pakornpiam/kumiko-lamp/stl/modern_shade_bishamon_kikkou.stl

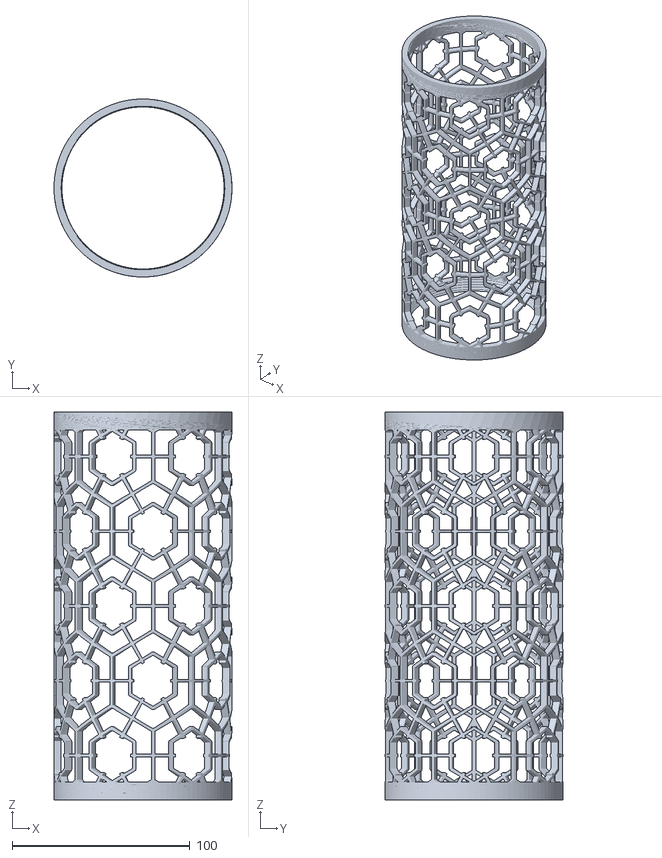
[picture p17: CAD file, 2026-08-05]
stl/modern_shade_bishamon_kikkou.stl
100.0 x 100.0 x 218.0
