pakornpiam/kumiko-lamp/stl/finial.stl

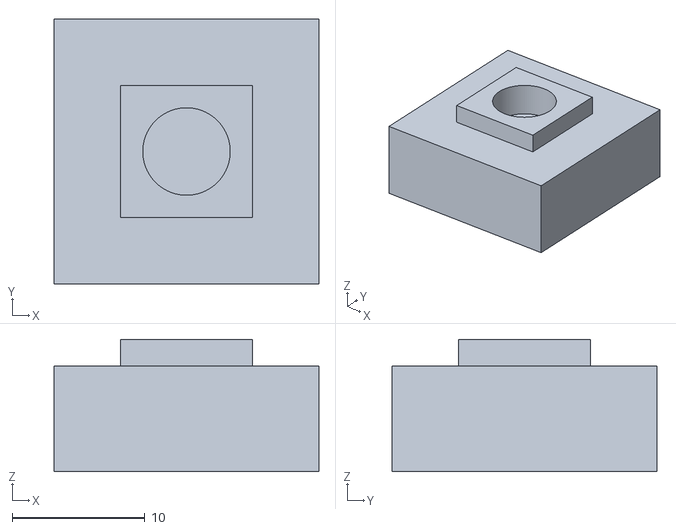
[picture p18: CAD file, 2026-08-05]
stl/finial.stl
20.0 x 20.0 x 10.0
