pakornpiam/kumiko-lamp/stl/panel_masu.stl

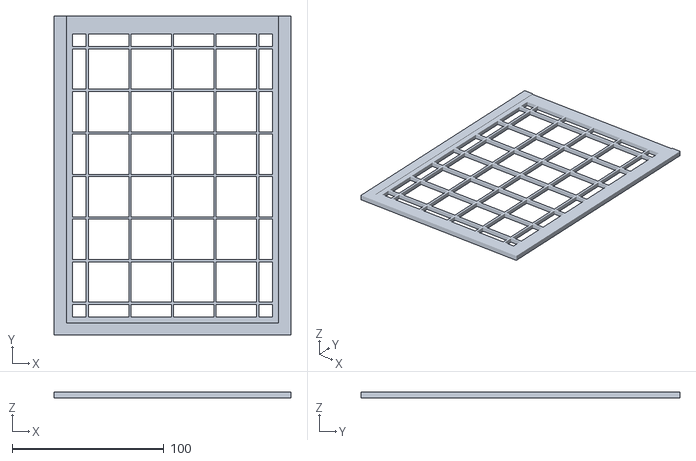
[picture p19: CAD file, 2026-08-03]
stl/panel_masu.stl
155.7 x 210.0 x 4.00
