pakornpiam/kumiko-lamp/stl/panel_senbon.stl

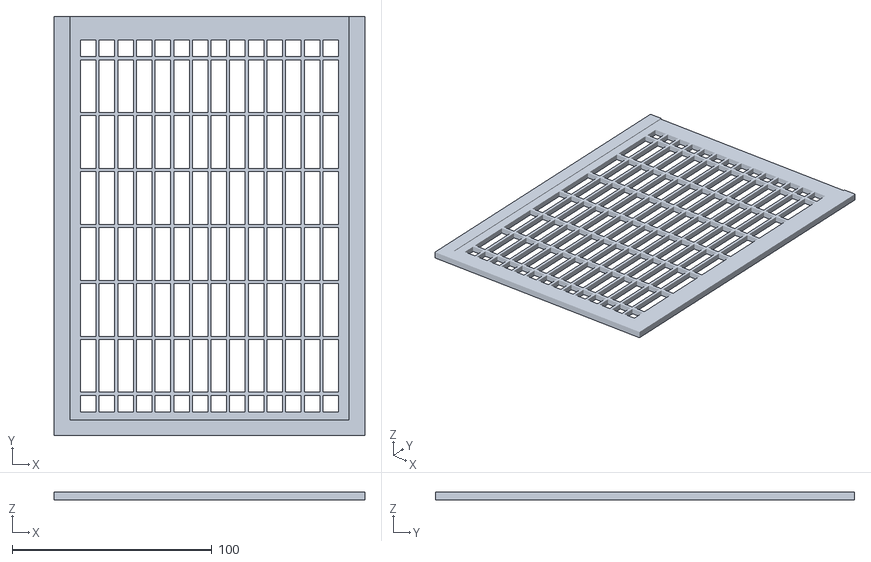
[picture p20: CAD file, 2026-08-03]
stl/panel_senbon.stl
155.7 x 210.0 x 4.00
