pakornpiam/kumiko-lamp/stl/panel_seigaiha.stl

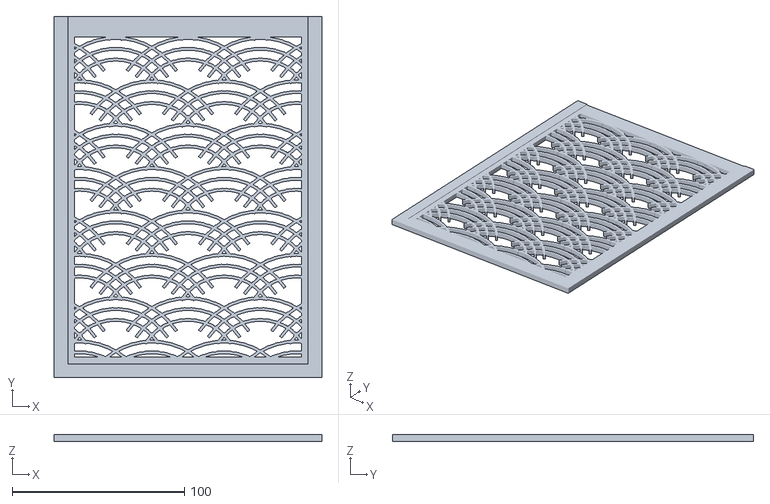
[picture p21: CAD file, 2026-08-03]
stl/panel_seigaiha.stl
155.7 x 210.0 x 4.00
