pakornpiam/kumiko-lamp/stl/diffuser_plate.stl

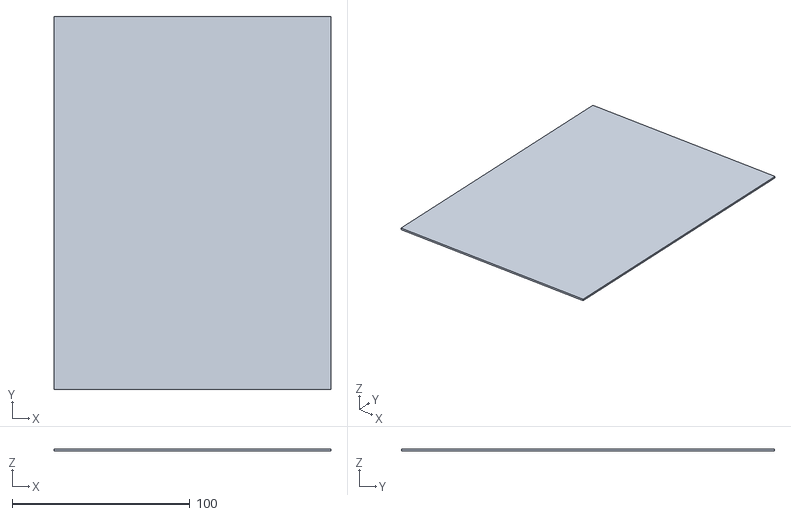
[picture p22: CAD file, 2026-08-02]
stl/diffuser_plate.stl
155.7 x 210.0 x 1.20
