pakornpiam/kumiko-lamp/stl/top_cap.stl

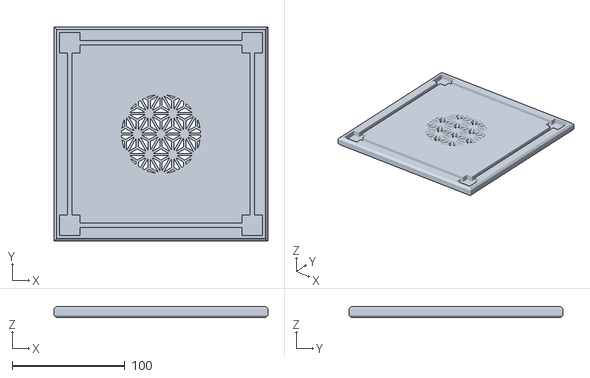
[picture p23: CAD file, 2026-08-02]
stl/top_cap.stl
190.0 x 190.0 x 10.0
