pakornpiam/kumiko-lamp/stl/base.stl

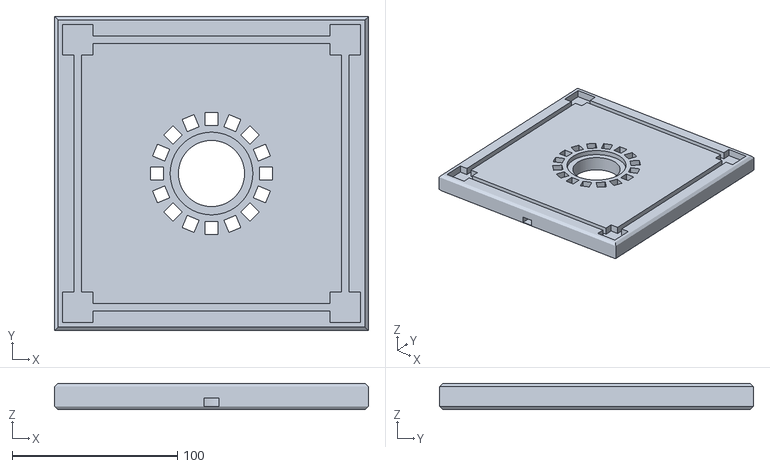
[picture p24: CAD file, 2026-08-02]
stl/base.stl
190.0 x 190.0 x 16.0
