pakornpiam/kumiko-lamp/stl/panel_dok_phut_tan.stl

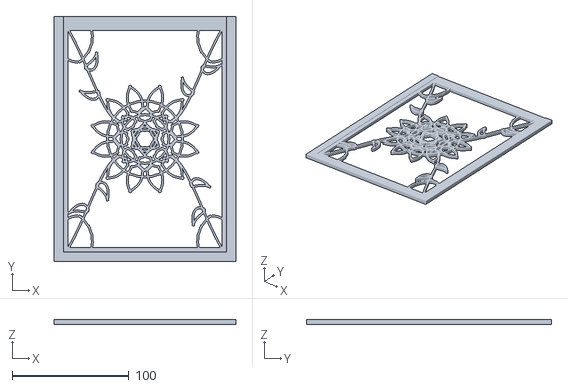
[picture p25: CAD file, 2026-07-31]
stl/panel_dok_phut_tan.stl
155.7 x 210.0 x 4.00
