pakornpiam/kumiko-lamp/stl/panel_kranok_kan_khot.stl

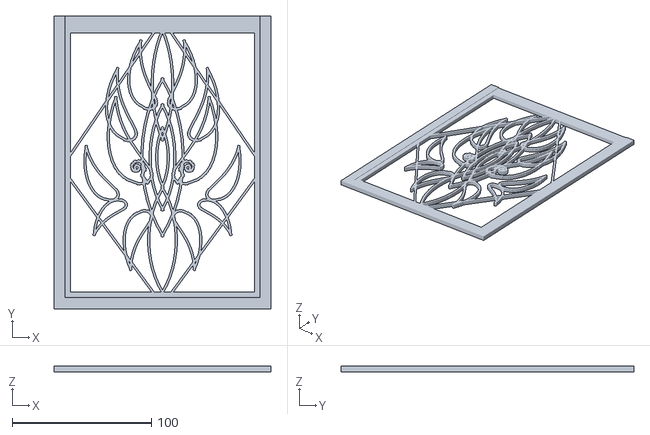
[picture p26: CAD file, 2026-07-31]
stl/panel_kranok_kan_khot.stl
155.7 x 210.0 x 4.00
