pakornpiam/kumiko-lamp/stl/leg.stl

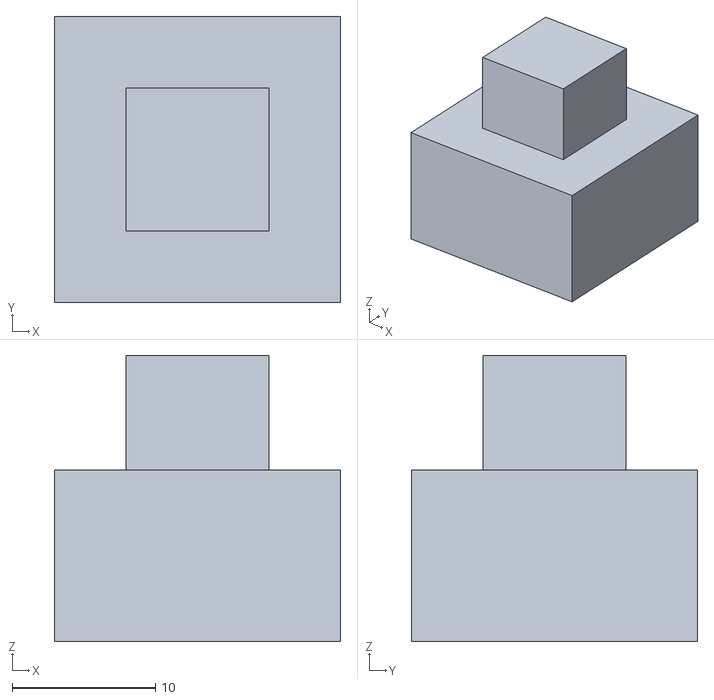
[picture p27: CAD file, 2026-07-30]
stl/leg.stl
20.0 x 20.0 x 20.0
