pakornpiam/kumiko-lamp/stl/panel_kagome.stl

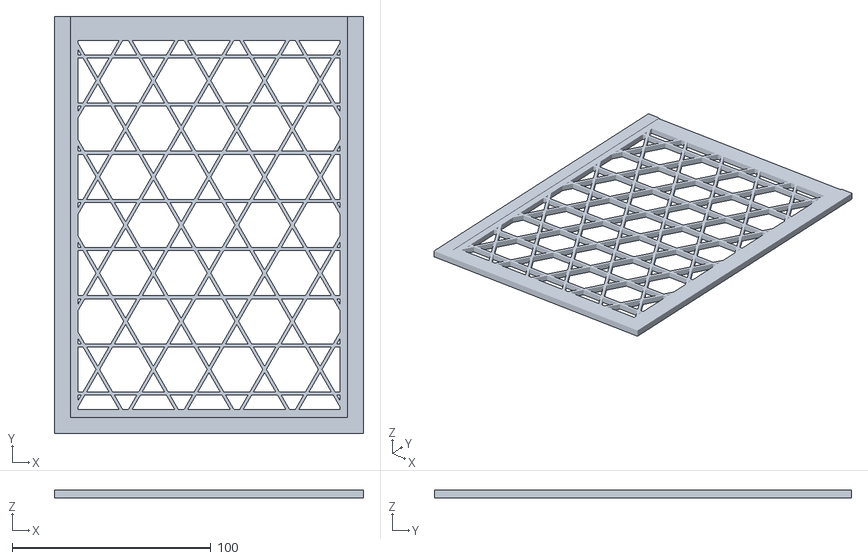
[picture p28: CAD file, 2026-07-30]
stl/panel_kagome.stl
155.7 x 210.0 x 4.00
