pakornpiam/kumiko-lamp/stl/panel_goma_gara.stl

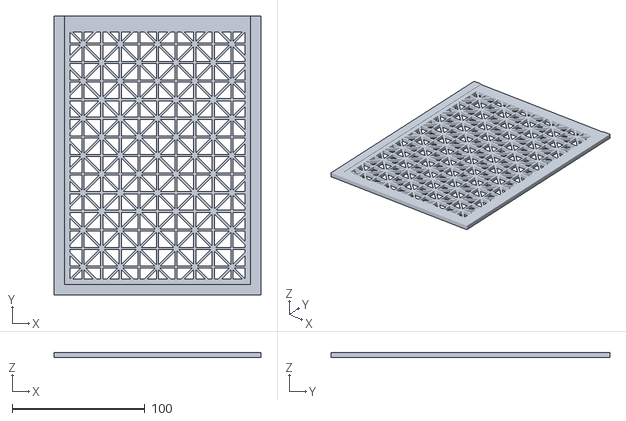
[picture p29: CAD file, 2026-07-30]
stl/panel_goma_gara.stl
155.7 x 210.0 x 4.00
