pakornpiam/kumiko-lamp/stl/panel_masu_tsunagi.stl

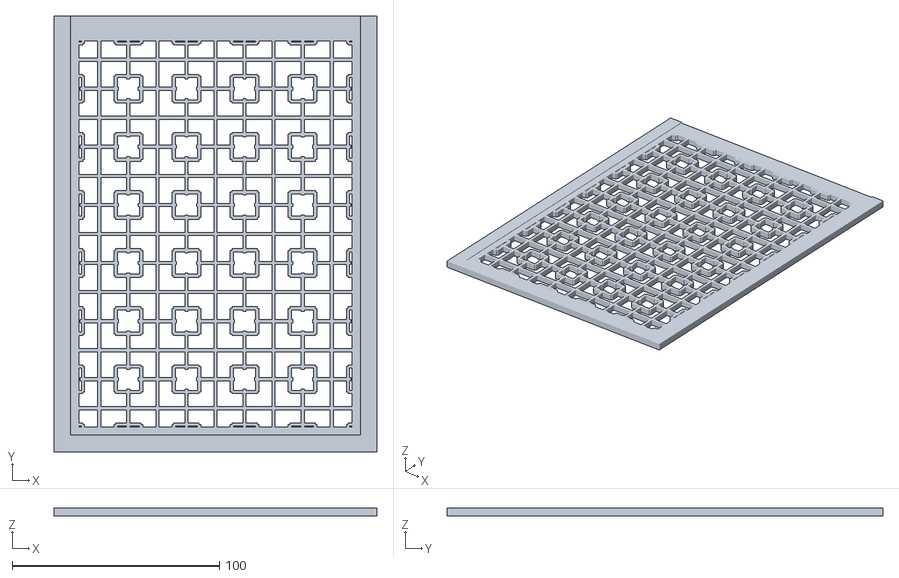
[picture p30: CAD file, 2026-07-30]
stl/panel_masu_tsunagi.stl
155.7 x 210.0 x 4.00
