pakornpiam/kumiko-lamp/stl/socket_adapter_ring.stl

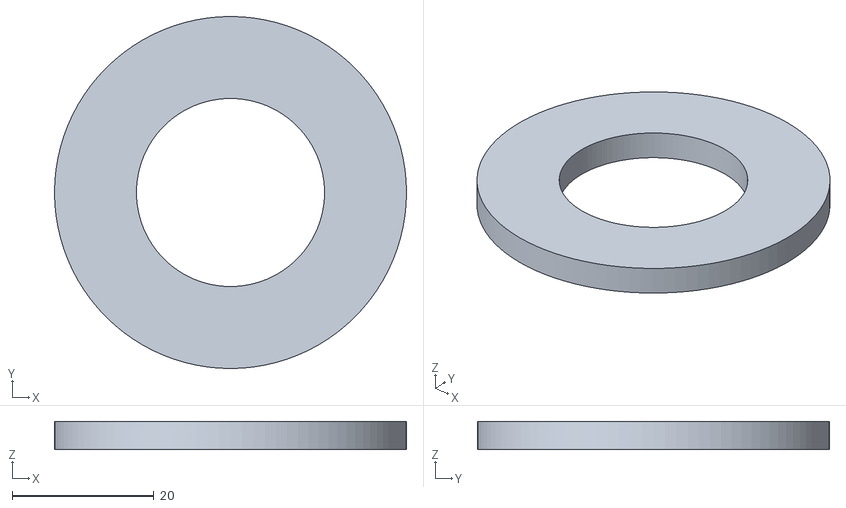
[picture p31: CAD file, 2026-07-28]
stl/socket_adapter_ring.stl
49.6 x 49.6 x 4.00
