pakornpiam/kumiko-lamp/stl/panel_asanoha.stl

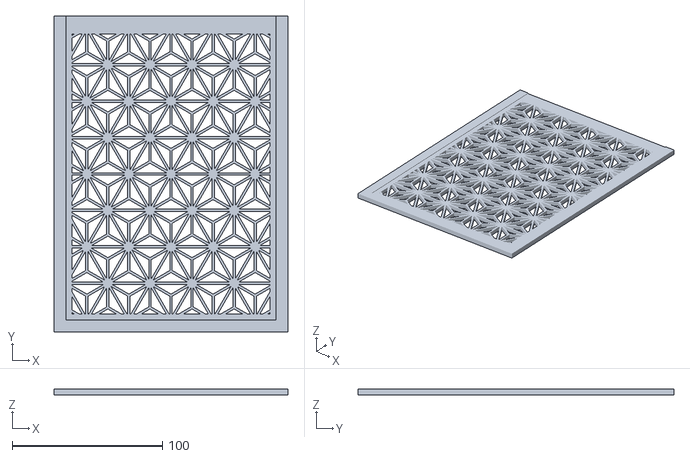
[picture p32: CAD file, 2026-07-28]
stl/panel_asanoha.stl
155.7 x 210.0 x 4.00
