pakornpiam/kumiko-lamp/stl/post.stl

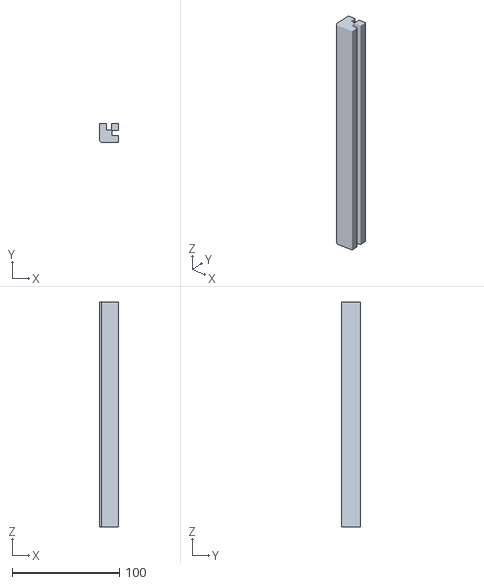
[picture p33: CAD file, 2026-07-28]
stl/post.stl
18.0 x 18.0 x 210.0
