pakornpiam/kumiko-lamp/stl/post_lower.stl

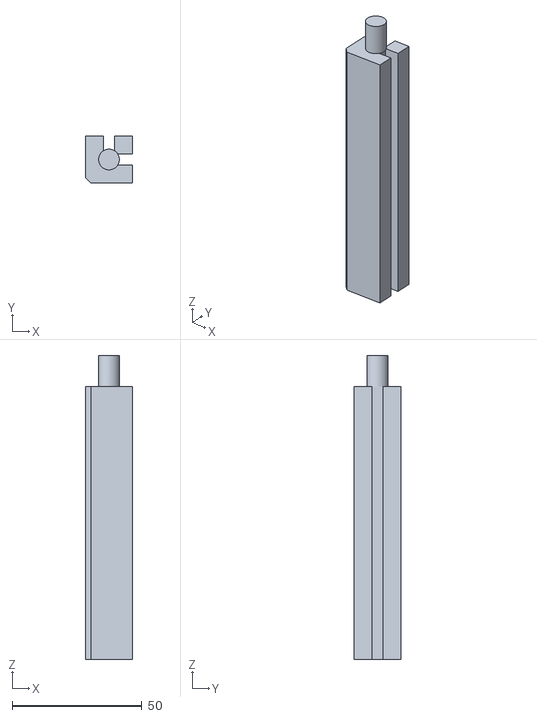
[picture p34: CAD file, 2026-07-28]
stl/post_lower.stl
18.0 x 18.0 x 117.0
