pakornpiam/kumiko-lamp/stl/panel_kikkou.stl

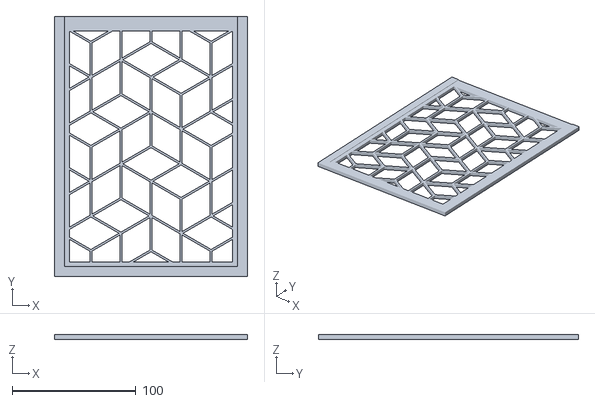
[picture p35: CAD file, 2026-07-28]
stl/panel_kikkou.stl
155.7 x 210.0 x 4.00
