pakornpiam/kumiko-lamp/stl/post_upper.stl

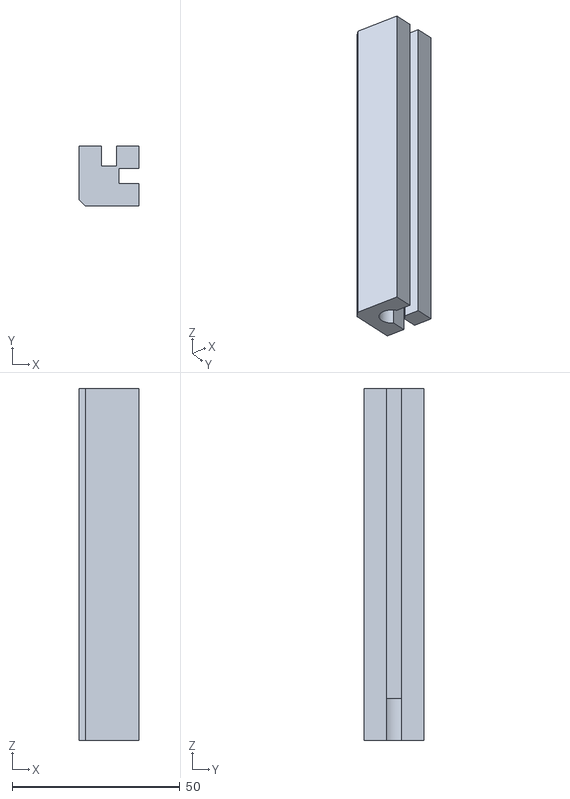
[picture p37: CAD file, 2026-07-28]
stl/post_upper.stl
18.0 x 18.0 x 105.0
